jharvey/Charge_Controller/Simulations/MOS_Heat_LTSpice/Heat_Sim_High_Side_Zoomed.png

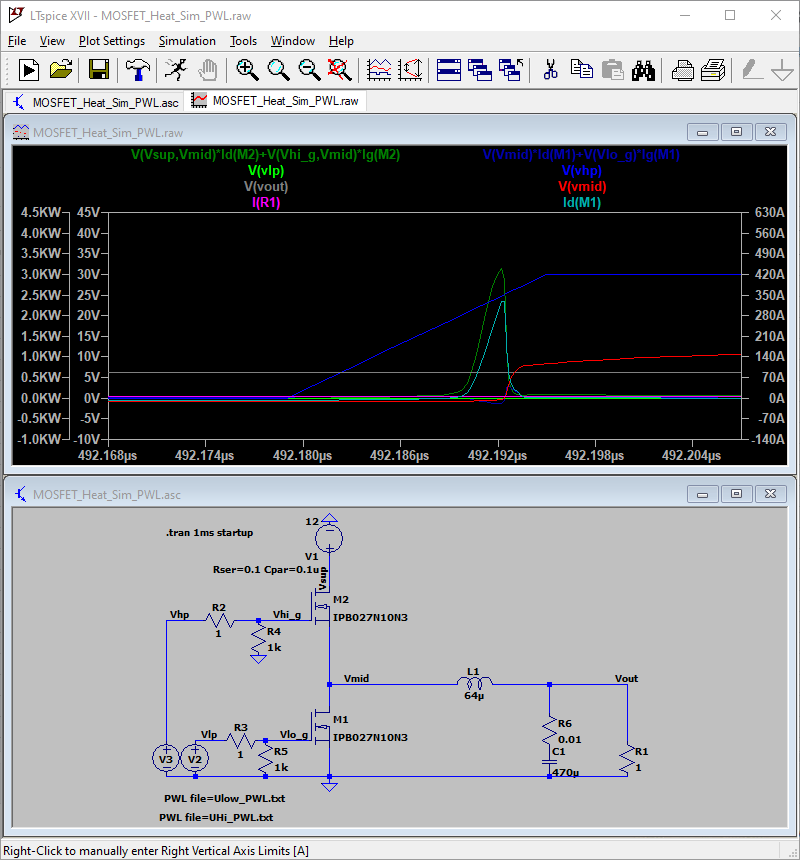
Simulations/MOS_Heat_LTSpice/Heat_Sim_High_Side_Zoomed.png
