jharvey/Charge_Controller/Simulations/MOS_Heat_LTSpice/HeatSim_Q2_0.31W_at_19Vin_with_2.5A_12V_Out_Batter_Charger.png

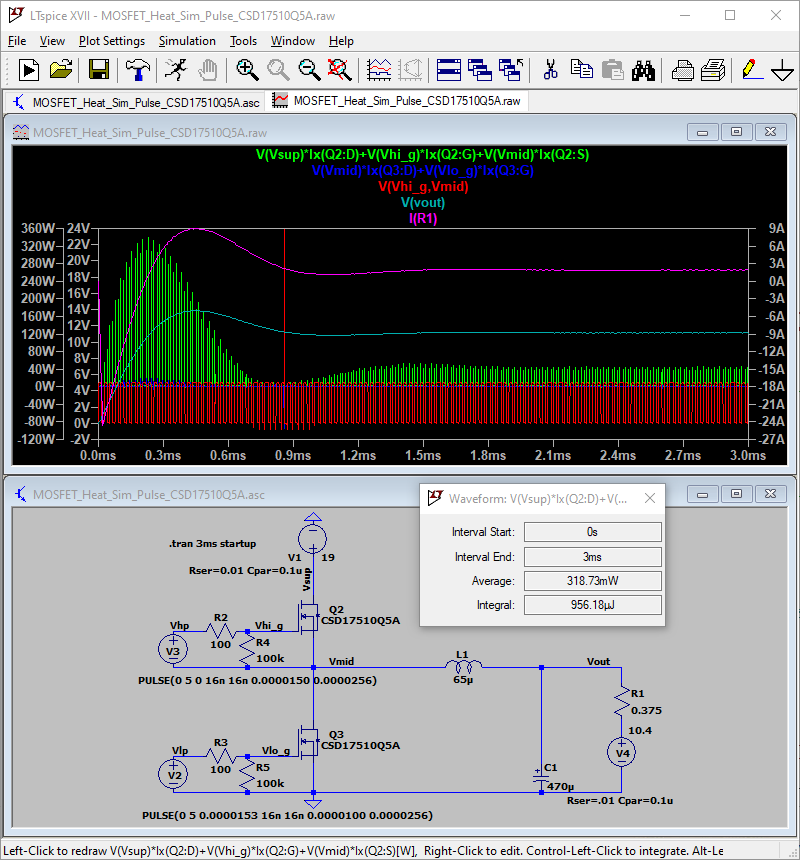
Simulations/MOS_Heat_LTSpice/HeatSim_Q2_0.31W_at_19Vin_with_2.5A_12V_Out_Batter_Charger.png
