jharvey/Charge_Controller/Simulations/MOS_Heat_LTSpice/HeatSim_Q2_4.78W_at_24Vin_with_27A_13.35V_Out_Batter_Charger.png

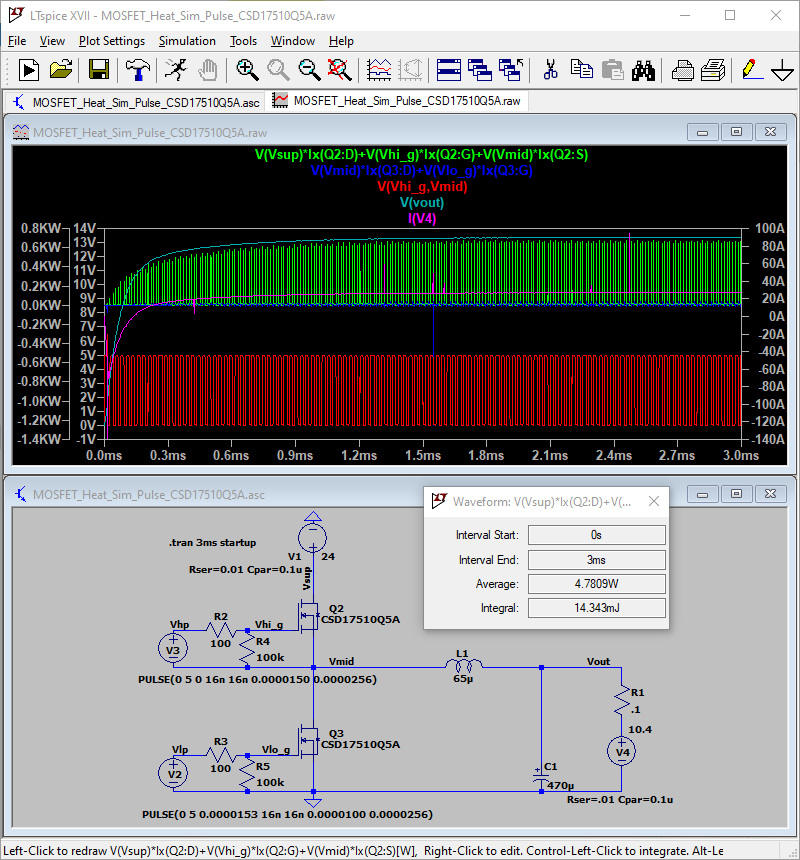
Simulations/MOS_Heat_LTSpice/HeatSim_Q2_4.78W_at_24Vin_with_27A_13.35V_Out_Batter_Charger.png
