jharvey/Charge_Controller/Simulations/MOS_Heat_LTSpice/MOSFET_Heat_Sim_Pulse3.png

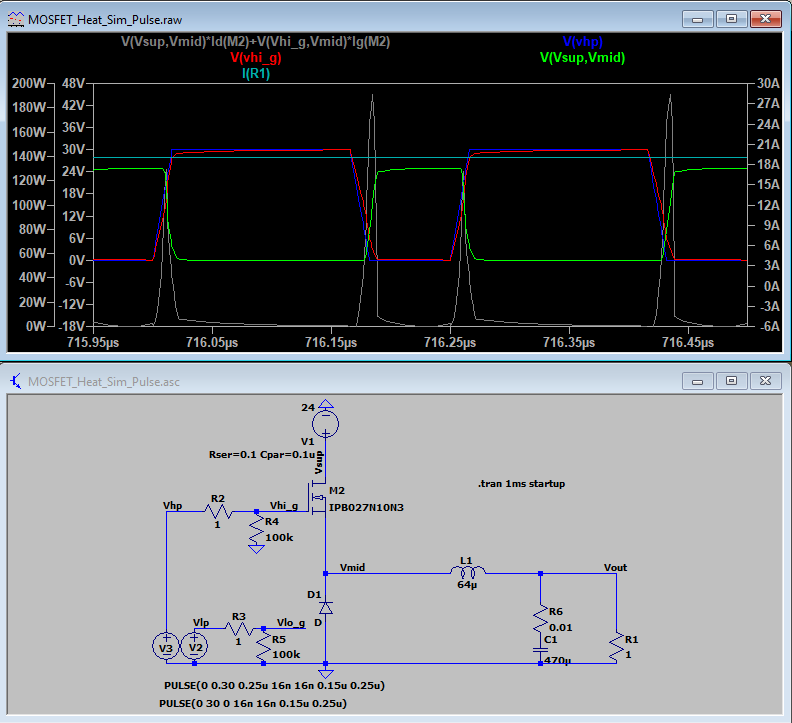
Simulations/MOS_Heat_LTSpice/MOSFET_Heat_Sim_Pulse3.png
