jharvey/Charge_Controller/Simulations/PCB_Toolkit_V8.21_2.5CperW.png

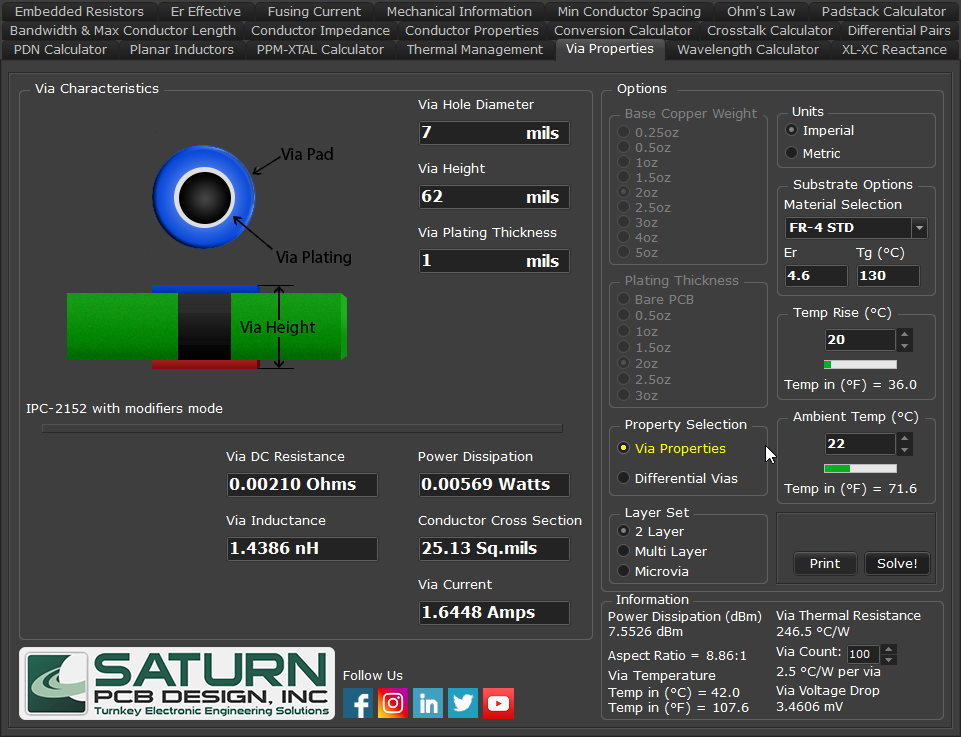
Simulations/PCB_Toolkit_V8.21_2.5CperW.png
