jharvey/Charge_Controller/Simulations/MOS_Heat_LTSpice/MOSFET_Heat_Sim_Pulse_IRFH5207_as_NCE8295AK.asc

C1: polcap; 470µ; V=100 Irms=1.88 Rser=0.013 Lser=6.47n mfg="Würth Elektronik" pn="860040880011 WCAP-ATUL 16x35,5" type="Al electrolytic"
L1: ind; 65µ; Ipk=17.2 Rser=0.01313 Rpar=21316 Cpar=20.57p mfg="Würth Elektronik" pn="7443783533650 WE-HCFT 3533"
Q2: nmos; IRFH5207
Q3: nmos; IRFH5207
R1: res; 0.375
R2: res; 100
R3: res; 100
R4: res; 100k
R5: res; 100k
V1: voltage; 30; Rser=0.01 Cpar=0.1u
V2: voltage; PULSE(0 5 0.0000153 16n 16n 0.0000100 0.0000256)
V3: voltage; PULSE(0 5 0 16n 16n 0.0000150 0.0000256)
V4: voltage; 10.4; Rser=.01 Cpar=0.1u
Named nets: 0, Vout, Vhi_g, Vlo_g, Vmid, Vhp, Vlp, Vsup
.tran 3ms startup
