jharvey/Charge_Controller/Simulations/MOS_Heat_LTSpice/MOSFET_Heat_Sim_PWL_CSD17510Q5A.asc

C1: cap; 470µ
D1: schottky; RBLQ3LAM10
D2: schottky; RBLQ3LAM10
L1: ind; 64µ
R1: res; 1
R2: res; 100
R3: res; 100
R4: res; 100k
R5: res; 100k
R6: res; 240m
U1: CSD17510Q5A
U2: CSD17510Q5A
V1: voltage; 30; Rser=0.1 Cpar=0.1u
V2: voltage; PWL file=Ulow_PWL.txt
V3: voltage; PWL file=UHi_PWL.txt
Named nets: 0, Vout, Vhi_g, Vlo_g, Vmid, Vhp, Vlp, Vsup
.tran 1ms startup
