jharvey/Charge_Controller/Simulations/MOS_Heat_LTSpice/MOSFET_Heat_Sim_PWL_CSD17510Q5A_2.asc

C1: polcap; 470µ; V=100 Irms=1.88 Rser=0.013 Lser=6.47n mfg="Würth Elektronik" pn="860040880011 WCAP-ATUL 16x35,5" type="Al electrolytic"
D1: schottky; RBLQ3LAM10
D2: schottky; RBLQ3LAM10
L1: ind; 65µ; Ipk=17.2 Rser=0.01313 Rpar=21316 Cpar=20.57p mfg="Würth Elektronik" pn="7443783533650 WE-HCFT 3533"
R1: res; 1
R2: res; 1
R3: res; 1
R4: res; 100k
R5: res; 100k
R6: res; 0
U1: CSD17510Q5A
U2: CSD17510Q5A
V1: voltage; 12; Rser=0.1 Cpar=0.1u
V2: voltage; PWL file=Ulow_PWL.txt
V3: voltage; PWL file=UHi_PWL.txt
Named nets: 0, Vout, Vhi_g, Vlo_g, Vmid, Vhp, Vlp, Vsup
.tran 0.1ms startup
