jharvey/Charge_Controller/Simulations/MOS_Heat_LTSpice/MOSFET_Heat_Sim_PWL.asc

C1: cap; 470µ
L1: ind; 64µ
M1: nmos; IPB027N10N3
M2: nmos; IPB027N10N3
R1: res; 1
R2: res; 1
R3: res; 1
R4: res; 1k
R5: res; 1k
R6: res; 0.01
V1: voltage; 12; Rser=0.1 Cpar=0.1u
V2: voltage; PWL(0 0 0.49m 0 0.5m 15 1m 15)
V3: voltage; PWL(0 0 0.249m 0 0.25m 15 0.49m 15 0.5m 0 0.749m 0 0.75m 15 1m 15)
Named nets: 0, Vout, Vhi_g, Vlo_g, Vmid, Vhp, Vlp, Vsup
.tran 1ms startup
